UCDElecSoc/25-26_Robot_Spider/Spider STLs/Leg - Long Arm.stl

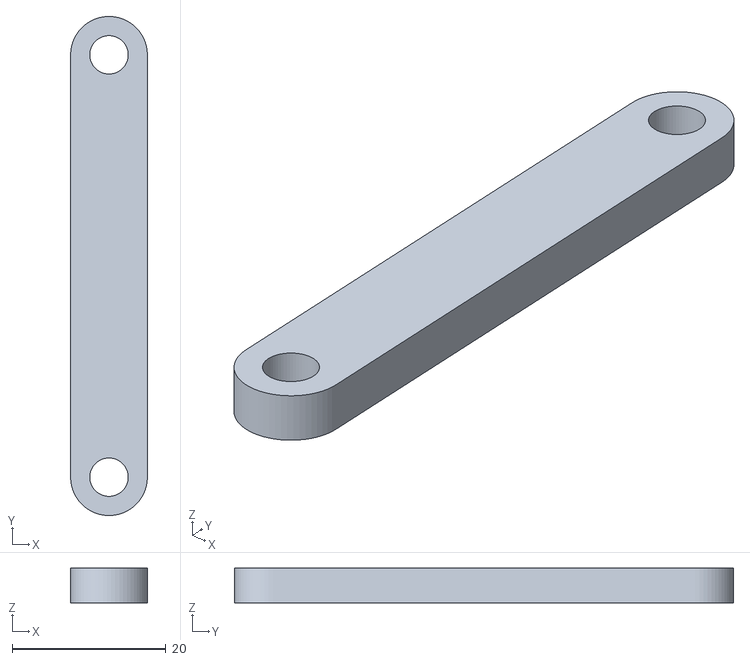
[picture p17: CAD file, 2026-03-24]
Spider STLs/Leg - Long Arm.stl
10.0 x 65.0 x 4.50
