UCDElecSoc/25-26_Robot_Spider/Spider STLs/Old Leg/Leg - Upper Leg.stl

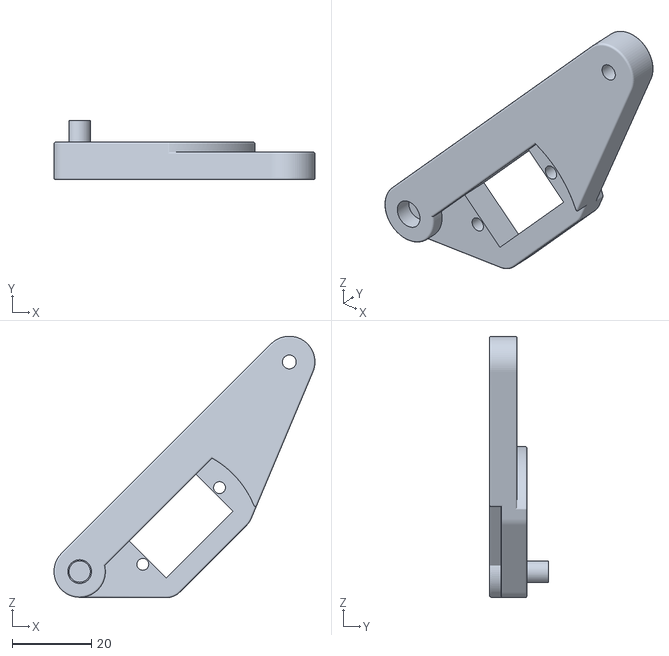
[picture p18: CAD file, 2026-03-24, an earlier design]
Spider STLs/Old Leg/Leg - Upper Leg.stl
66.0 x 15.0 x 66.1
