UCDElecSoc/25-26_Robot_Spider/Spider STLs/Old Leg/Leg - Upper Beam.stl

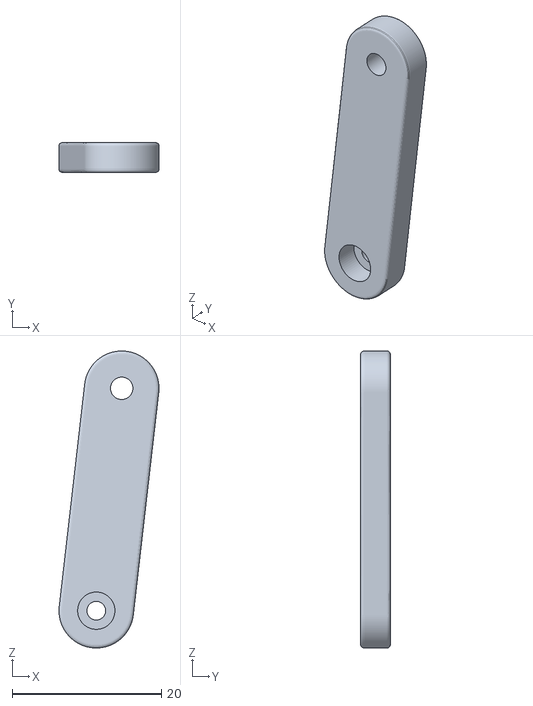
[picture p19: CAD file, 2026-03-24, an earlier design]
Spider STLs/Old Leg/Leg - Upper Beam.stl
13.4 x 4.00 x 39.8
