UCDElecSoc/25-26_Robot_Spider/Spider STLs/Old Leg/Leg - Lower Beam.stl

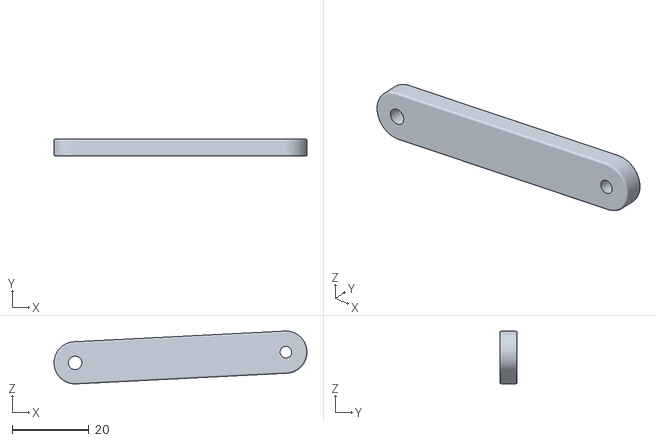
[picture p20: CAD file, 2026-03-24, an earlier design]
Spider STLs/Old Leg/Leg - Lower Beam.stl
65.9 x 4.50 x 13.8
